njtromp/cato/factory.js

"use strict";

var Constants = {
    OFF: 0,
    ON: 1
}

var I2C = require("i2c");
var PWM = require("./pwm");
var PulseSensor = require('./pulse-sensor');
var RPMController = require('./rpm-controller');
var GPSDListener = require('./gpsd-listener');
var RawNMEAListener = require('./raw-nmea-listener');
var LogController =  require('./log-controller');
var DelayedSwitch = require('./delayed-switch');
var GPIO = require('onoff').Gpio;
var config = require('./config.json');
var InfoServer = require('./server/info-server')

function Factory() {}

/**
 * Creates a RPM controller that can be used to control the RPM.
 * The RPM controller uses a PWM and a PulseSensor instance which are also created.
 */
Factory.prototype.createRPMController = function() {
	var pwm = new PWM(config.PWM);
	var pulseSensor = new PulseSensor(config.PulseSensor);
    var voltageReductionSwitch = createVoltageReductionSwitch();
	return new RPMController(config.RPM, pwm, pulseSensor, voltageReductionSwitch);
}

/**
 * Creates a log controller that takes care of passing speed updates to the log-motor.
 * The LogController uses a GPSDListener and a RPMController instance which are also created.
 */
Factory.prototype.createLogController = function() {
    var rpmController = this.createRPMController();
    var logController = new LogController(rpmController);
    var gpsdListener = new GPSDListener(config.GPSD, logController);
    return logController;
}

Factory.prototype.createRawNMEAListener = function() {
    var rawNMEAListener = new RawNMEAListener(config.GPSD);
    return rawNMEAListener;
}

Factory.prototype.createServer = function() {
    var infoServer = new InfoServer(config.Server, this.createRawNMEAListener());
    infoServer.startServer();
}

function createVoltageReductionSwitch() {
    var voltageReductionSwitch = new GPIO(config.PowerSwitch.switchPin, 'out');
    var onFunction = function(rpmController) {
        if (config.PowerSwitch.debug) {
            console.log('Flipping the power switch to ON');
        }
        voltageReductionSwitch.writeSync(Constants.ON);
        if (rpmController) {
            rpmController.switchingToLowVoltage();
        }
    };
    var offFunction = function(rpmController) {
        if (config.PowerSwitch.debug) {
            console.log('Flipping the power switch to OFF');
        }
        voltageReductionSwitch.writeSync(Constants.OFF);
        if (rpmController) {
            rpmController.switchingToHighVoltage()
        }
    };
    // Wrap the actual powerswitch in a delayed switch
    // this will ensure that the power is not switched on and off every control interval
    return new DelayedSwitch(config.PowerSwitch, onFunction, offFunction);
}

module.exports = Factory;
